FroggyCorp/Light_Light/src/sound.h

//Copyright (c) 2025 Froggy / FroggyCorp.
//Do what you want with it until it's not money

const uint16_t music_animation_lancement_jeu[] = {
    330, 0, 392, 0, 440, 0, 392, 0, 330, 0, 392, 0, 440, 0, 392, 0,
    294, 0, 370, 0, 392, 0, 370, 0, 294, 0, 370, 0, 392, 0, 370, 0,
    261, 0, 330, 0, 392, 0, 330, 0, 261, 0, 330, 0, 392, 0, 330, 0,
    247, 0, 294, 0, 370, 0, 294, 0, 247, 0, 294, 0, 370, 0, 294, 0,
    220, 0, 261, 0, 330, 0, 261, 0, 220, 0, 261, 0, 330, 0, 261, 0,
    196, 0, 247, 0, 294, 0, 247, 0, 196, 0, 247, 0, 294, 0, 247, 0
};    

const uint16_t music_animation_gagnant[] = {392, 392, 0, 523, 523, 0, 659, 659, 0, 784, 784, 0, 0, 659, 784, 784, 784, 784, 784, 0, 0, 0};
